crispy25/OpenBook/Images/Display.png

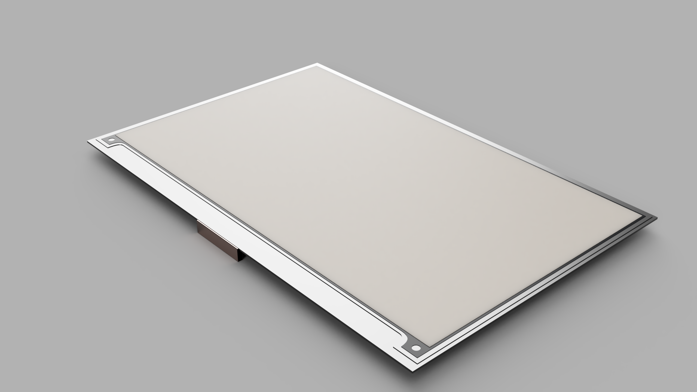
Images/Display.png
